jamro/brass-thumb-pomodoro/model/stl/gauge_slider.stl

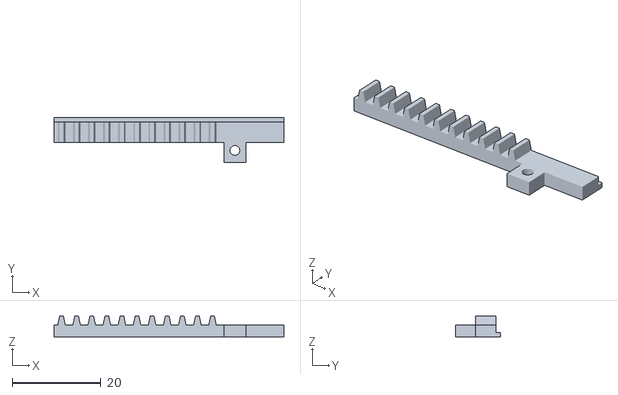
[picture p18: CAD file, 2024-07-20]
model/stl/gauge_slider.stl
51.8 x 10.2 x 4.70
